monemone-org/mone_numpad/keyboard-layout-editor/monenumpad.png

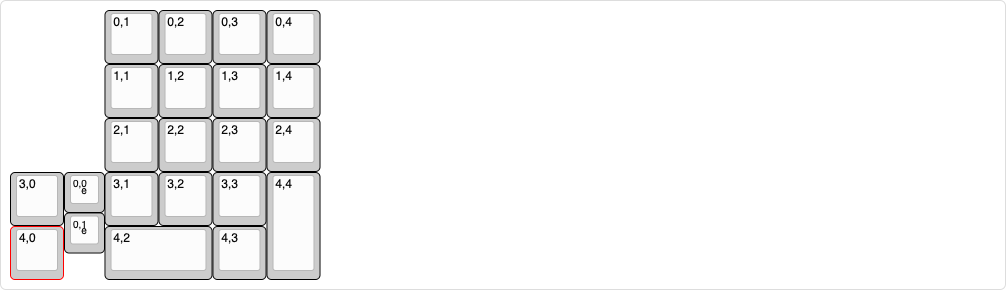
keyboard-layout-editor/monenumpad.png
